yatush/ha-7inch-display/backgrounds/modern-background-with-lines (1).jpg

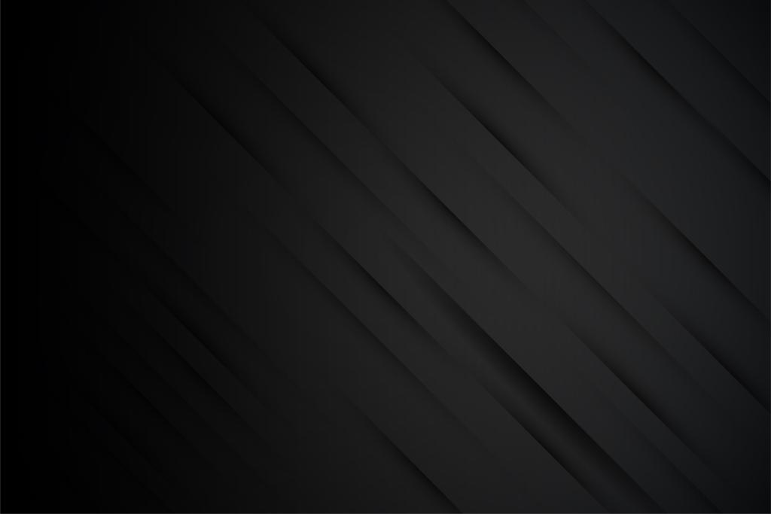
backgrounds/modern-background-with-lines (1).jpg
