yatush/ha-7inch-display/backgrounds/pexels-adrien-olichon-2387793 (1).jpg

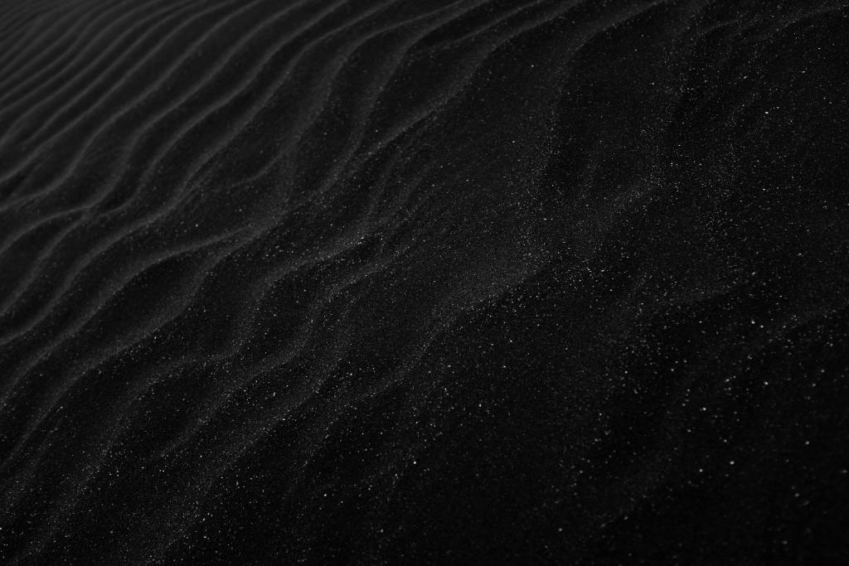
backgrounds/pexels-adrien-olichon-2387793 (1).jpg
