yatush/ha-7inch-display/backgrounds/pexels-adrien-olichon-2931286 (1).jpg

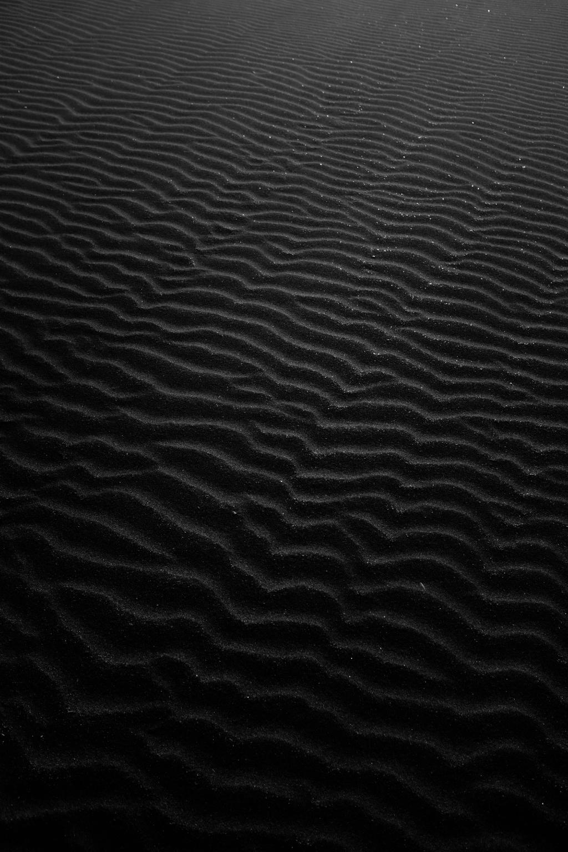
backgrounds/pexels-adrien-olichon-2931286 (1).jpg
