yatush/ha-7inch-display/backgrounds/pexels-adrien-olichon-3709434 (1).jpg

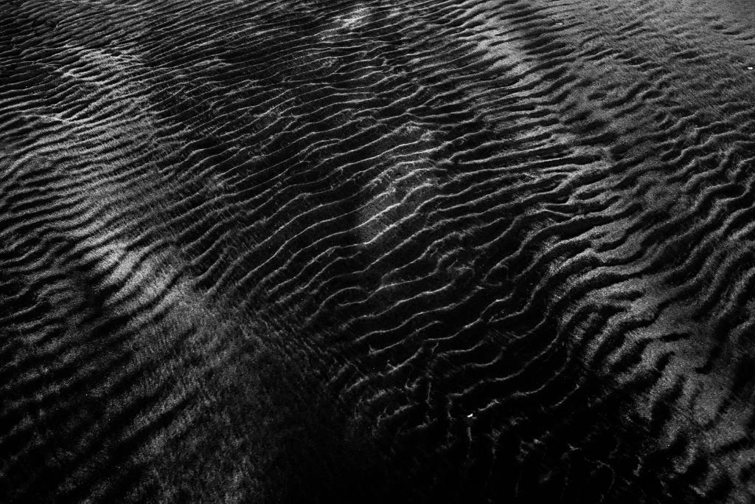
backgrounds/pexels-adrien-olichon-3709434 (1).jpg
