yatush/ha-7inch-display/backgrounds/pexels-beyzanur-k-18864357 (1).jpg

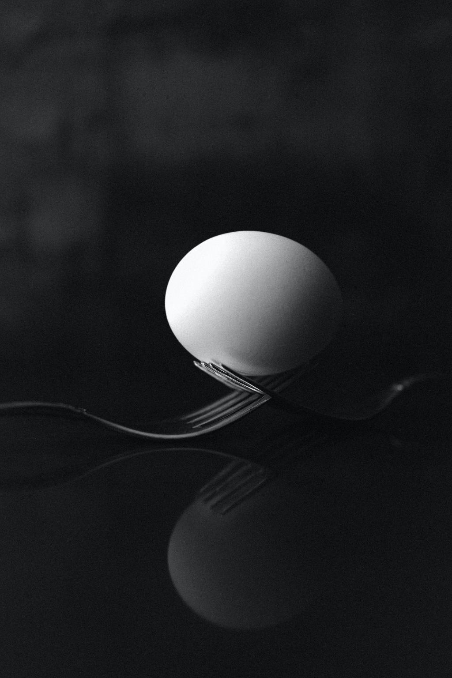
backgrounds/pexels-beyzanur-k-18864357 (1).jpg
