yatush/ha-7inch-display/backgrounds/pexels-brett-sayles-959284 (1).jpg

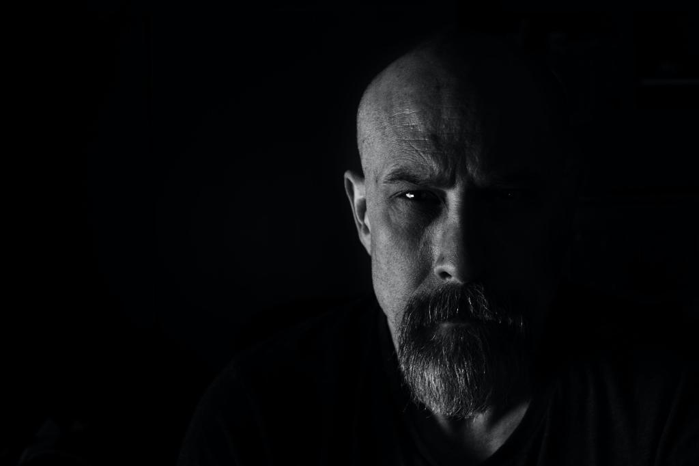
backgrounds/pexels-brett-sayles-959284 (1).jpg
