yatush/ha-7inch-display/backgrounds/pexels-eberhard-grossgasteiger-2098428 (1).jpg

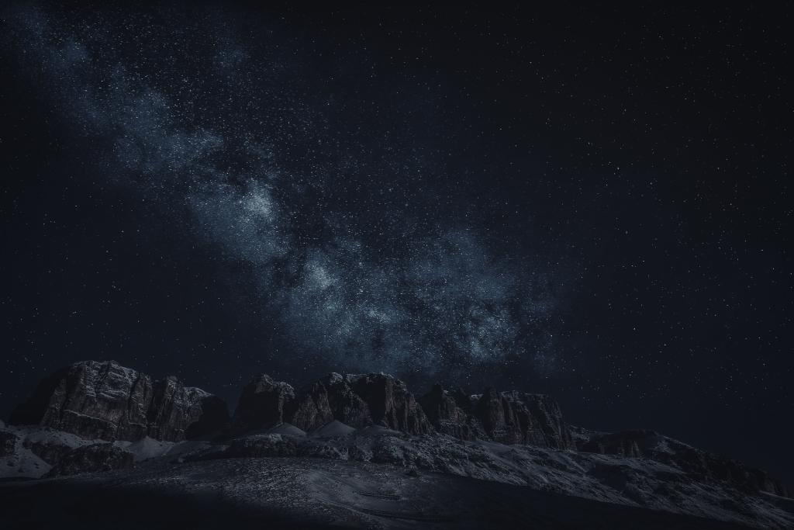
backgrounds/pexels-eberhard-grossgasteiger-2098428 (1).jpg
