yatush/ha-7inch-display/backgrounds/pexels-edson-habacuc-rafael-904332 (1).jpg

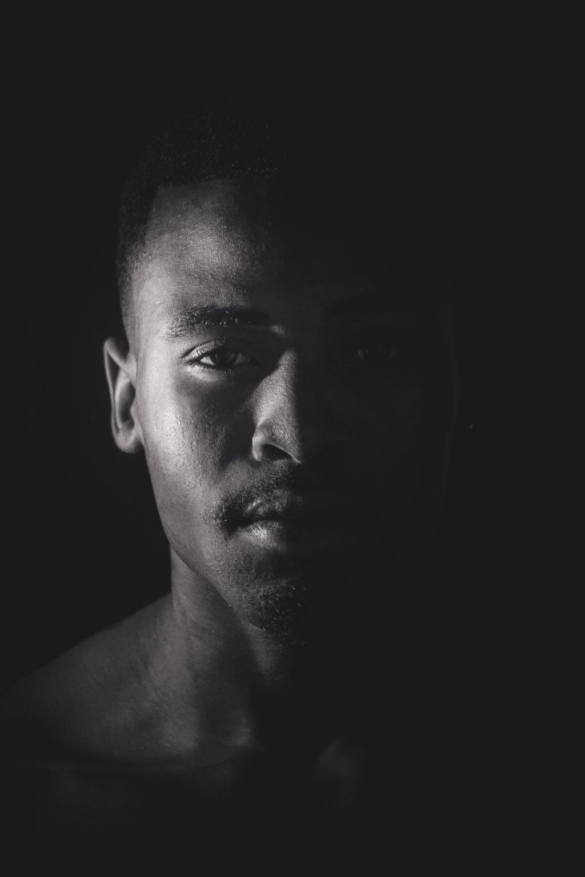
backgrounds/pexels-edson-habacuc-rafael-904332 (1).jpg
