yatush/ha-7inch-display/backgrounds/pexels-emma-li-5199173 (1).jpg

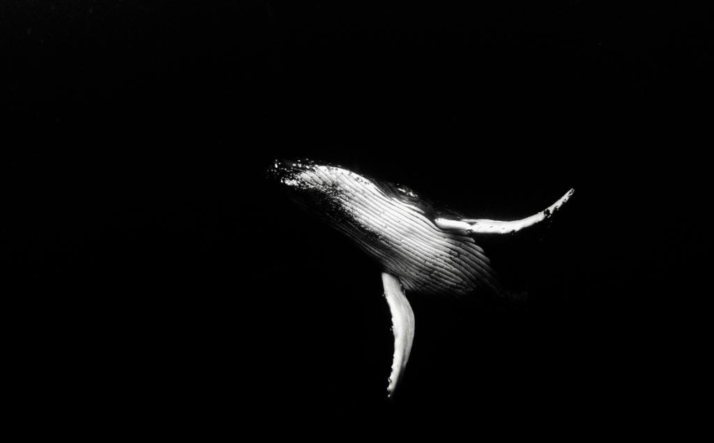
backgrounds/pexels-emma-li-5199173 (1).jpg
