yatush/ha-7inch-display/backgrounds/pexels-mathias-reding-4394232 (1).jpg

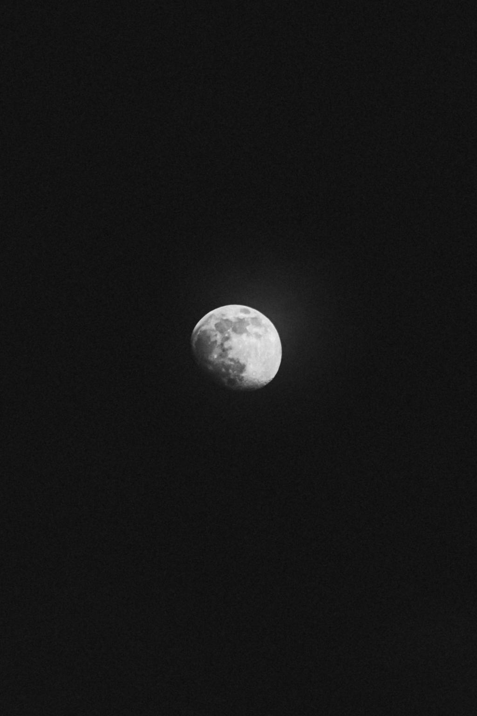
backgrounds/pexels-mathias-reding-4394232 (1).jpg
