yatush/ha-7inch-display/backgrounds/pexels-mohamed-abdelsadig-2967140 (1).jpg

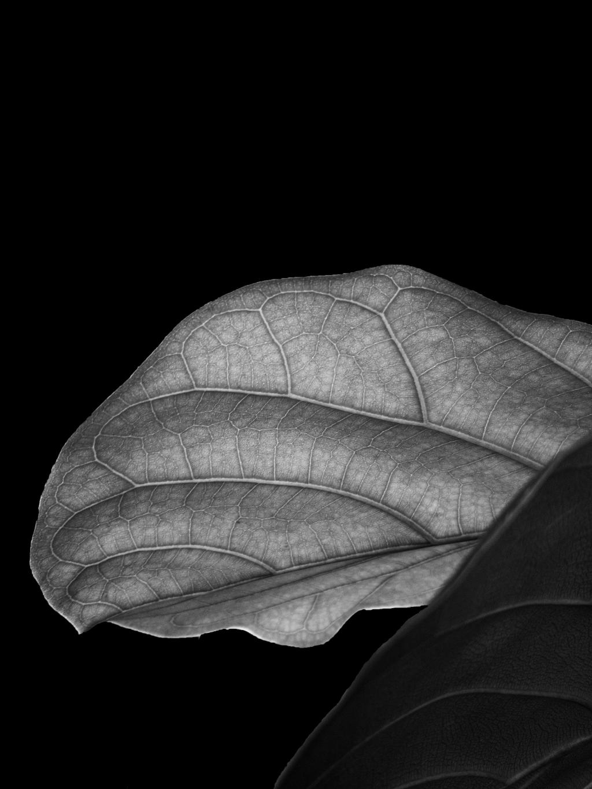
backgrounds/pexels-mohamed-abdelsadig-2967140 (1).jpg
