yatush/ha-7inch-display/backgrounds/pexels-pixabay-261985 (1).jpg

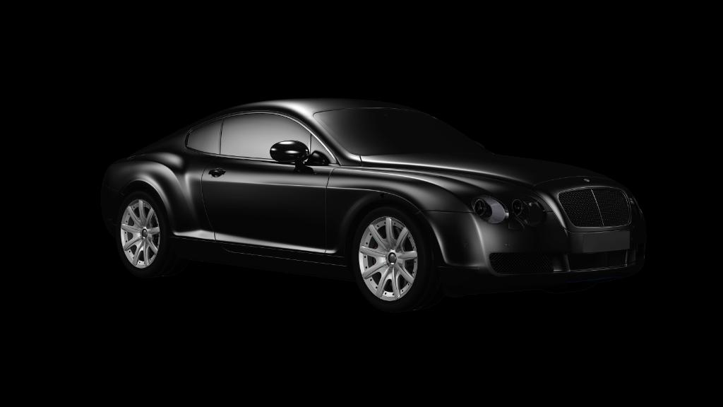
backgrounds/pexels-pixabay-261985 (1).jpg
