yatush/ha-7inch-display/backgrounds/pexels-pixabay-355757 (1).jpg

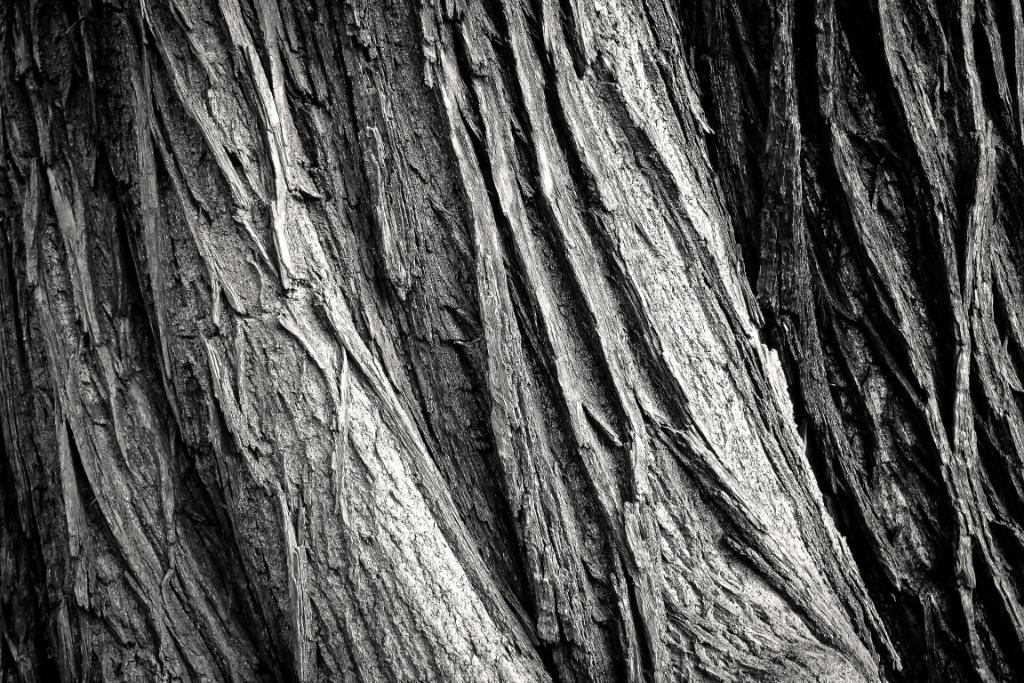
backgrounds/pexels-pixabay-355757 (1).jpg
