yatush/ha-7inch-display/backgrounds/pexels-toni-cuenca-619419 (1).jpg

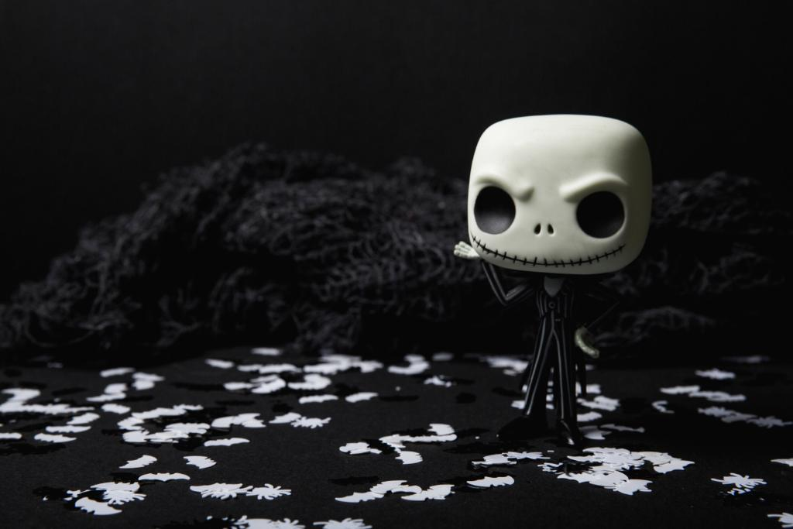
backgrounds/pexels-toni-cuenca-619419 (1).jpg
