yatush/ha-7inch-display/backgrounds/solid-concrete-wall-textured-backdrop (1).jpg

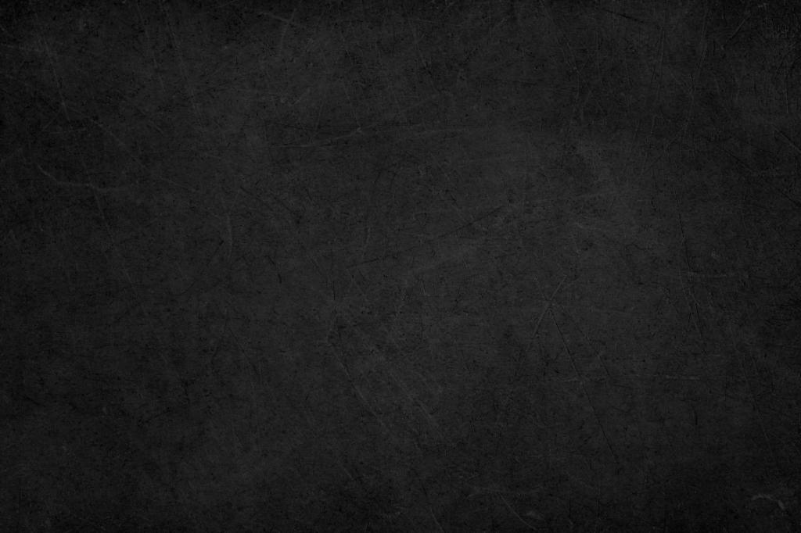
backgrounds/solid-concrete-wall-textured-backdrop (1).jpg
